ernestasga/leonardo-joystick/parts/Connectors.png

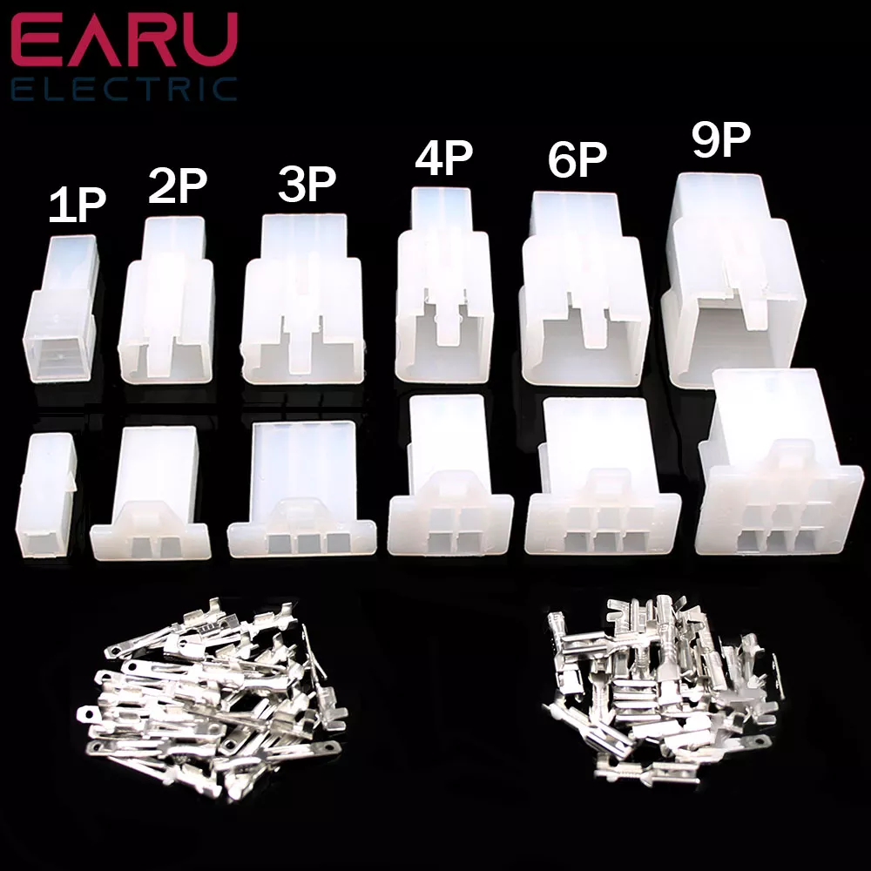
parts/Connectors.png
