ernestasga/leonardo-joystick/parts/Slider Potentiometer.png

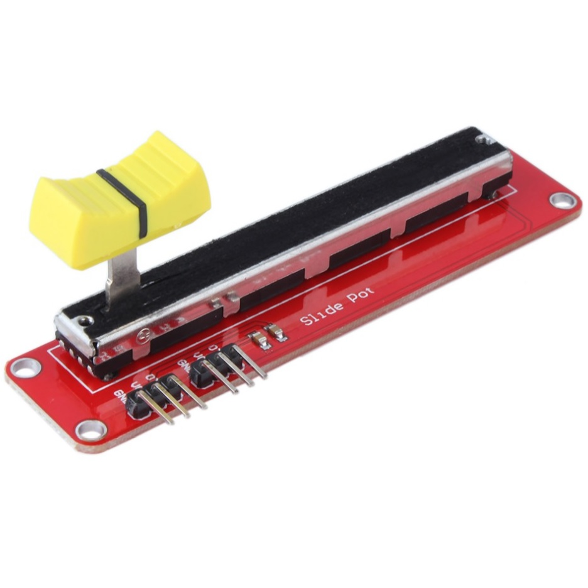
parts/Slider Potentiometer.png
